blazer82/gb.fpga/src/hdl/verilogboy/clk_div.v

`timescale 1ns / 1ns
`default_nettype wire
//////////////////////////////////////////////////////////////////////////////////
// Company:
// Engineer: Wenting Zhang
//
// Create Date:    09:50:37 04/07/2018
// Module Name:    clk_div
// Project Name:   VerilogBoy
// Description:
//
// Dependencies:
//
// Additional Comments:
//
//////////////////////////////////////////////////////////////////////////////////
module clk_div(
    input i,
    output reg o = 0
    );

    parameter WIDTH = 15, DIV = 1000;

    reg [WIDTH - 1:0] counter = 0;

    always @(posedge i)
    begin
        if (counter == (DIV / 2 - 1)) begin
            o <= ~o;
            counter <= 0;
        end
        else
            counter <= counter + 1'b1;
    end
endmodule
